sentry5588/two_wheeler/balancing_robot/global.h

/*
  global.h - Library for creating global variables
  Created by sentry5588, Apr 2019
  MIT license
*/

#define FORWARD 1
#define BACKRWARD 0

#ifndef global_h
#define global_h

#include <LinkedList.h>

// (m/s^2) local gravitational acceleration
extern const double g;

////////////////////// control variables declaration

// ====================================================================
// the measurement from sensor to the controller
// --------------------------------------------------------------------
// the state variable for the robot
// [roll, pitch, yaw, d_roll, d_pitch, d_yaw]
// The robot should not have non-zero roll position on a flat surface
// d_roll, d_pitch, d_yaw: angular velocities in roll, pitch, and yaw
extern double s[6];
extern double s_GOSI[6];
extern double s_AO[6];
extern double s_CF[6];

// ====================================================================
// the control actions from controller to actuators
// --------------------------------------------------------------------
// To do

// To do: external double s[6];

// ====================================================================
// Debug variables
// --------------------------------------------------------------------
// Output data in linked list
extern LinkedList<double> debug_list;
// An counter as an indicator of the CPU idle time
extern unsigned long idle_loop_count;

#endif
